HomeSmartMesh/nrf52_thread_sensortag/firmware/07_tag_zephyr_button/src/main.c

#include <zephyr.h>
#include <device.h>
#include <drivers/gpio.h>
#include <logging/log.h>

LOG_MODULE_REGISTER(main, LOG_LEVEL_INF);

#define SW0_NODE	DT_ALIAS(sw0)

#if DT_NODE_HAS_STATUS(SW0_NODE, okay)
#define SW0_GPIO_LABEL	DT_GPIO_LABEL(SW0_NODE, gpios)
#define SW0_GPIO_PIN	DT_GPIO_PIN(SW0_NODE, gpios)
#define SW0_GPIO_FLAGS	(GPIO_INPUT | DT_GPIO_FLAGS(SW0_NODE, gpios))
#else
#error "Unsupported board: sw0 devicetree alias is not defined"
#define SW0_GPIO_LABEL	""
#define SW0_GPIO_PIN	0
#define SW0_GPIO_FLAGS	0
#endif

#define SLEEP_TIME_MS   1000

static struct gpio_callback button_cb_data;

void button_pressed(const struct device *dev, struct gpio_callback *cb,
		    uint32_t pins)
{
	LOG_INF("Button pressed at %" PRIu32 "\n", k_cycle_get_32());
}

void init_button()
{
	const struct device *button;
	int ret;
	button = device_get_binding(SW0_GPIO_LABEL);
	if (button == NULL) {
		LOG_ERR("Error: didn't find %s device\n", SW0_GPIO_LABEL);
		return;
	}

	ret = gpio_pin_configure(button, SW0_GPIO_PIN, SW0_GPIO_FLAGS);
	if (ret != 0) {
		LOG_ERR("Error %d: failed to configure %s pin %d\n",
		       ret, SW0_GPIO_LABEL, SW0_GPIO_PIN);
		return;
	}

	ret = gpio_pin_interrupt_configure(button,
					   SW0_GPIO_PIN,
					   GPIO_INT_EDGE_TO_ACTIVE);
	if (ret != 0) {
		LOG_ERR("Error %d: failed to configure interrupt on %s pin %d\n",
			ret, SW0_GPIO_LABEL, SW0_GPIO_PIN);
		return;
	}

	gpio_init_callback(&button_cb_data, button_pressed, BIT(SW0_GPIO_PIN));
	gpio_add_callback(button, &button_cb_data);
	LOG_INF("Set up button at %s pin %d\n", SW0_GPIO_LABEL, SW0_GPIO_PIN);
}

void main(void)
{
	LOG_INF("Hello from Sensor Tag Button example");

	init_button();

	int count = 0;
	while (1) {
		k_msleep(SLEEP_TIME_MS);
		LOG_INF("loop: %d",count++);
	}
}
